czbiohub-sf/ULC-OD-Meter/ODMeter_KiCAD/ODMeter.sch

## KiCad design ODMeter_KiCAD/ODMeter.sch (2021-09-01)

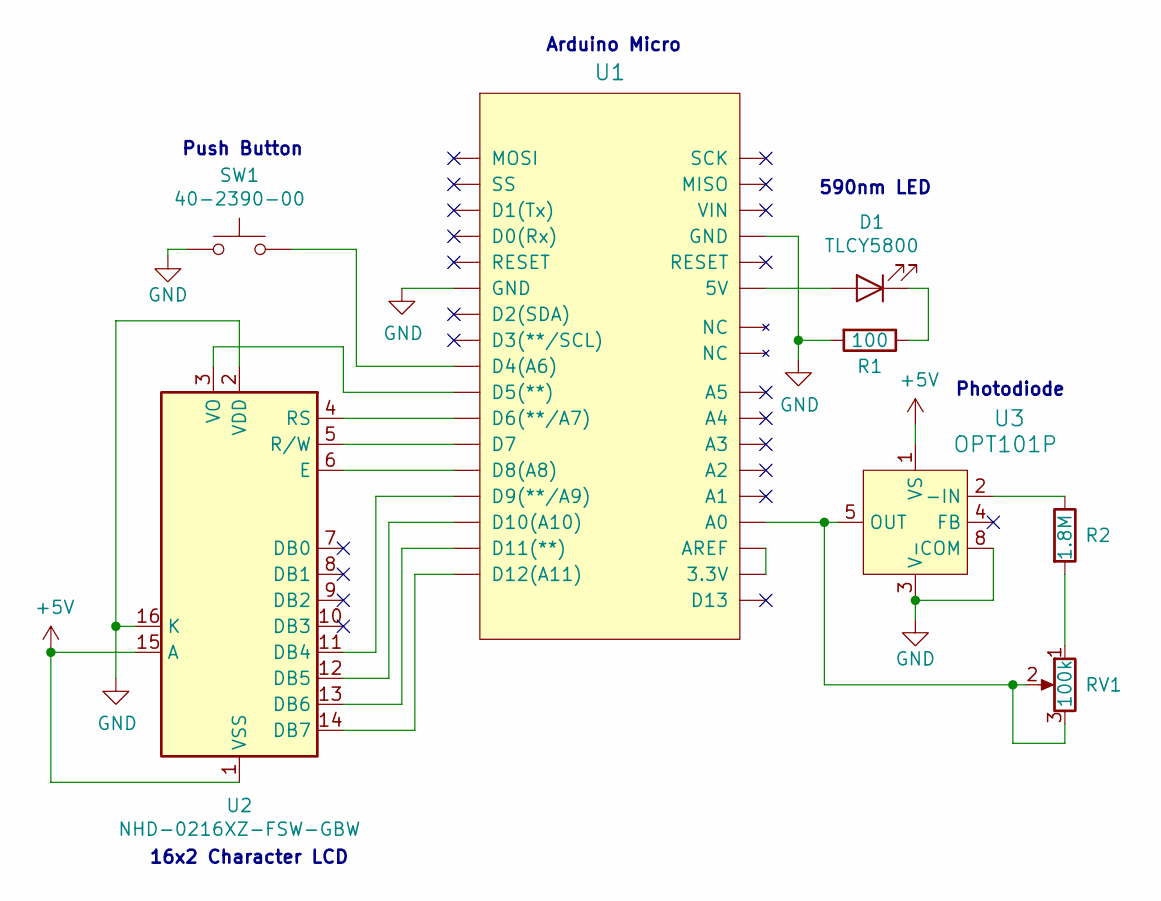
[picture p7: schematic ODMeter.sch]

Parts:
D1: TLCY5800
R1: 100
R2: 1.8M
RV1: 100k
SW1: 40-2390-00
U1: ArduinoMicro
U2: NHD-0216XZ-FSW-GBW; NHD-0420H1Z
U3: OPT101P; DIP-8_W7.62mm; MPN OPT101P; Digi-Key_PN 296-23090-5-ND

Connections:
+5V: U2.1 (VSS), U2.15 (A), U3.1 (VS)
GND: R1.2, SW1.1, U1.~, U2.2 (VDD), U2.16 (K), U3.3 (V-), U3.8 (COM)
unnamed: D1.1 (K), R1.1
unnamed: D1.2 (A), U1.~
unnamed: R2.1, U3.2 (-IN)
unnamed: R2.2, RV1.1
unnamed: RV1.2, RV1.3, U1.~, U3.5 (OUT)
unnamed: SW1.2, U1.~
unnamed: U1.~, U2.3 (VO), U2.4 (RS), U2.5 (R/W), U2.6 (E), U2.11 (DB4), U2.12 (DB5), U2.13 (DB6), U2.14 (DB7)

Notes on the sheet:
590nm LED
16x2 Character LCD
Arduino Micro
Push Button
Photodiode
